hollie/netnode/firmware/pic18f/utility_monitor/fuses.h

//////////////////////////////////////////////////////////////////
// Device configuration section
// For PIC18F25X0 on netnode hardware v1


#ifdef __18F2580_H
// For 18F2580
#pragma config OSC = IRCIO67, IESO = OFF, FCMEN = OFF
#pragma config PWRT = ON, BOREN = OFF
#pragma config WDT = OFF, WDTPS = 32768
#pragma config MCLRE = ON, LPT1OSC = OFF, PBADEN = OFF
#pragma config DEBUG = OFF, LVP = OFF, STVREN = ON, XINST = OFF
#pragma config CP0 = OFF, CP1 = OFF, CP2 = OFF, CP3 = OFF
#pragma config CPB = OFF, CPD = OFF
#pragma config WRT0 = OFF, WRT1 = OFF, WRT2 = OFF, WRT3 = OFF
#pragma config WRTB = OFF, WRTC = OFF, WRTD = OFF
#pragma config EBTR0 = OFF, EBTR1 = OFF, EBTR2 = OFF, EBTR3 = OFF
#pragma config EBTRB = OFF
#endif
#ifdef __18F2520_H
// For 18F2520
#pragma config OSC = INTIO67, IESO = OFF, FCMEN = OFF
#pragma config PWRT = ON, BOREN = OFF
#pragma config WDT = OFF, WDTPS = 32768
#pragma config MCLRE = ON, LPT1OSC = OFF, PBADEN = OFF
#pragma config DEBUG = OFF, LVP = OFF, STVREN = ON, XINST = OFF
#pragma config CP0 = OFF, CP1 = OFF, CP2 = OFF, CP3 = OFF
#pragma config CPB = OFF, CPD = OFF
#pragma config WRT0 = OFF, WRT1 = OFF, WRT2 = OFF, WRT3 = OFF
#pragma config WRTB = OFF, WRTC = OFF, WRTD = OFF
#pragma config EBTR0 = OFF, EBTR1 = OFF, EBTR2 = OFF, EBTR3 = OFF
#pragma config EBTRB = OFF
#endif
#ifdef __18F45K80_H
// CONFIG1L
#pragma config RETEN = OFF      // VREG Sleep Enable bit (Ultra low-power regulator is Disabled (Controlled by REGSLP bit))
#pragma config INTOSCSEL = LOW  // LF-INTOSC Low-power Enable bit (LF-INTOSC in Low-power mode during Sleep)
#pragma config SOSCSEL = DIG    // SOSC Power Selection and mode Configuration bits (Digital (SCLKI) mode)
#pragma config XINST = ON       // Extended Instruction Set (Enabled)

// CONFIG1H
#pragma config FOSC = HS2       // Oscillator (EC oscillator (Medium power, 160 kHz - 16 MHz))
#pragma config PLLCFG = ON      // PLL x4 Enable bit (Disabled)
#pragma config FCMEN = ON       // Fail-Safe Clock Monitor (Enabled)
#pragma config IESO = OFF       // Internal External Oscillator Switch Over Mode (Disabled)

// CONFIG2L
#pragma config PWRTEN = OFF     // Power Up Timer (Disabled)
#pragma config BOREN = SBORDIS  // Brown Out Detect (Enabled in hardware, SBOREN disabled)
#pragma config BORV = 3         // Brown-out Reset Voltage bits (1.8V)
#pragma config BORPWR = ZPBORMV // BORMV Power level (ZPBORMV instead of BORMV is selected)

// CONFIG2H
#pragma config WDTEN = OFF      // Watchdog Timer (WDT disabled in hardware; SWDTEN bit disabled)
#pragma config WDTPS = 1048576  // Watchdog Postscaler (1:1048576)

// CONFIG3H
#pragma config CANMX = PORTB    // ECAN Mux bit (ECAN TX and RX pins are located on RB2 and RB3, respectively)
#pragma config MSSPMSK = MSK7   // MSSP address masking (7 Bit address masking mode)
#pragma config MCLRE = ON       // Master Clear Enable (MCLR Enabled, RE3 Disabled)

// CONFIG4L
#pragma config STVREN = ON      // Stack Overflow Reset (Enabled)
#pragma config BBSIZ = BB1K     // Boot Block Size (1K word Boot Block size)

// CONFIG5L
#pragma config CP0 = OFF        // Code Protect 00800-01FFF (Disabled)
#pragma config CP1 = OFF        // Code Protect 02000-03FFF (Disabled)
#pragma config CP2 = OFF        // Code Protect 04000-05FFF (Disabled)
#pragma config CP3 = OFF        // Code Protect 06000-07FFF (Disabled)

// CONFIG5H
#pragma config CPB = OFF        // Code Protect Boot (Disabled)
#pragma config CPD = OFF        // Data EE Read Protect (Disabled)

// CONFIG6L
#pragma config WRT0 = OFF       // Table Write Protect 00800-03FFF (Disabled)
#pragma config WRT1 = OFF       // Table Write Protect 04000-07FFF (Disabled)
#pragma config WRT2 = OFF       // Table Write Protect 08000-0BFFF (Disabled)
#pragma config WRT3 = OFF       // Table Write Protect 0C000-0FFFF (Disabled)

// CONFIG6H
#pragma config WRTC = OFF       // Config. Write Protect (Disabled)
#pragma config WRTB = OFF       // Table Write Protect Boot (Disabled)
#pragma config WRTD = OFF       // Data EE Write Protect (Disabled)

// CONFIG7L
#pragma config EBTR0 = OFF      // Table Read Protect 00800-03FFF (Disabled)
#pragma config EBTR1 = OFF      // Table Read Protect 04000-07FFF (Disabled)
#pragma config EBTR2 = OFF      // Table Read Protect 08000-0BFFF (Disabled)
#pragma config EBTR3 = OFF      // Table Read Protect 0C000-0FFFF (Disabled)

// CONFIG7H
#pragma config EBTRB = OFF      // Table Read Protect Boot (Disabled)
#endif
